MikeZ7/LF_Hammerhead/KiCAD/LF_HAMMERHEAD_schematics.kicad_sch

## KiCad design KiCAD/LF_HAMMERHEAD_schematics.kicad_sch (2023-11-29)

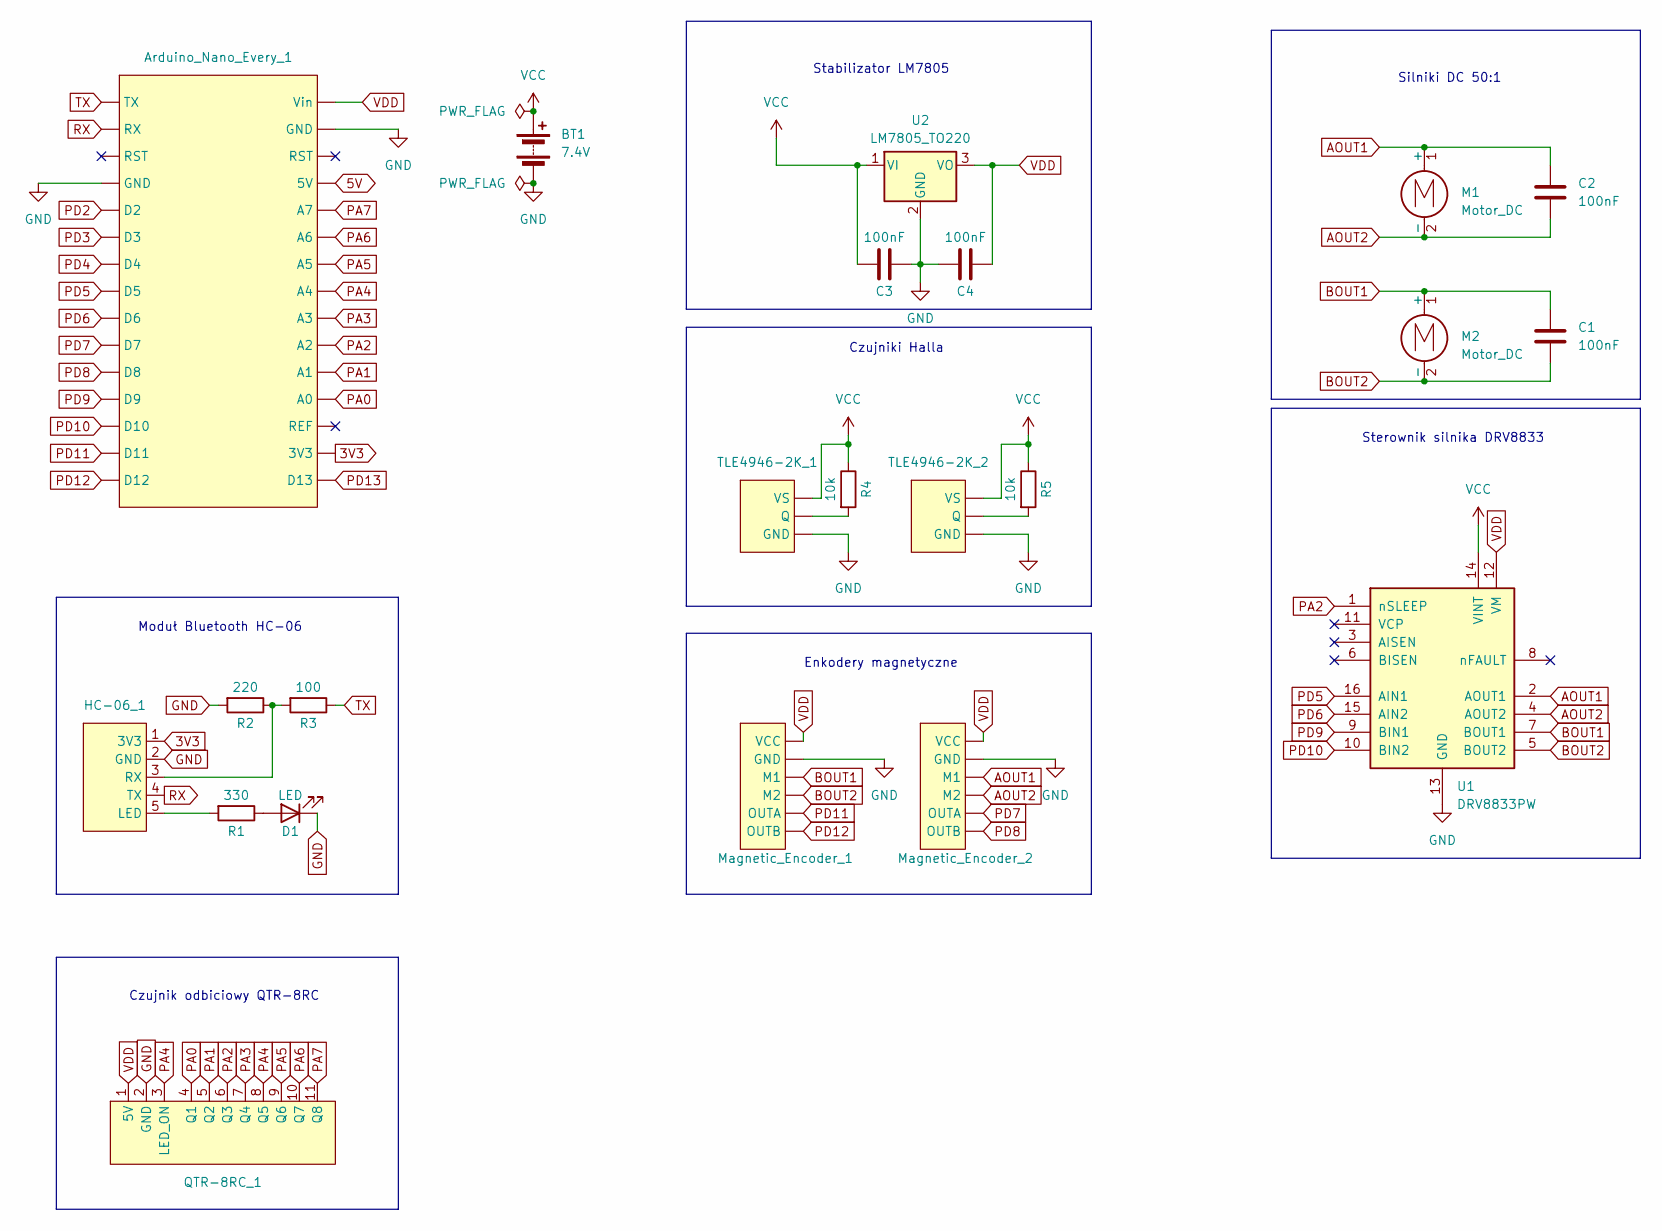
[picture p8: schematic LF_HAMMERHEAD_schematics.kicad_sch]

Parts:
Arduino_Nano_Every_1: (no value)
BT1: 7.4V
C1, C2, C3, C4: 100nF
D1: LED
HC-06_1: (no value)
M1, M2: Motor_DC
Magnetic_Encoder_1, Magnetic_Encoder_2: (no value)
QTR-8RC_1: (no value)
R1: 330
R2: 220
R3: 100
R4, R5: 10k
TLE4946-2K_1, TLE4946-2K_2: (no value)
U1: DRV8833PW; TSSOP-16_4.4x5mm_P0.65mm
U2: LM7805_TO220; TO-220-3_Vertical

Connections:
3V3: Arduino_Nano_Every_1., HC-06_1.1 (3V3)
5V: Arduino_Nano_Every_1.
AOUT1: C2.1, M1.1 (+), Magnetic_Encoder_2., U1.2 (AOUT1)
AOUT2: C2.2, M1.2 (-), Magnetic_Encoder_2., U1.4 (AOUT2)
BOUT1: C1.1, M2.1 (+), Magnetic_Encoder_1., U1.7 (BOUT1)
BOUT2: C1.2, M2.2 (-), Magnetic_Encoder_1., U1.5 (BOUT2)
GND: Arduino_Nano_Every_1., BT1.2 (-), C3.2, C4.1, D1.1 (K), HC-06_1.2 (GND), Magnetic_Encoder_1., Magnetic_Encoder_2., QTR-8RC_1.2 (GND), R2.2, TLE4946-2K_1., TLE4946-2K_2., U1.13 (GND), U2.2 (GND)
unnamed: D1.2 (A), R1.1
unnamed: HC-06_1.3 (RX), R2.1, R3.2
unnamed: HC-06_1.5 (LED), R1.2
unnamed: R4.2, TLE4946-2K_1.
unnamed: R5.2, TLE4946-2K_2.
PA0: Arduino_Nano_Every_1., QTR-8RC_1.4 (Q1)
PA1: Arduino_Nano_Every_1., QTR-8RC_1.5 (Q2)
PA2: Arduino_Nano_Every_1., QTR-8RC_1.6 (Q3), U1.1 (nSLEEP)
PA3: Arduino_Nano_Every_1., QTR-8RC_1.7 (Q4)
PA4: Arduino_Nano_Every_1., QTR-8RC_1.3 (LED_ON), QTR-8RC_1.8 (Q5)
PA5: Arduino_Nano_Every_1., QTR-8RC_1.9 (Q6)
PA6: Arduino_Nano_Every_1., QTR-8RC_1.10 (Q7)
PA7: Arduino_Nano_Every_1., QTR-8RC_1.11 (Q8)
PD2: Arduino_Nano_Every_1.
PD3: Arduino_Nano_Every_1.
PD4: Arduino_Nano_Every_1.
PD5: Arduino_Nano_Every_1., U1.16 (AIN1)
PD6: Arduino_Nano_Every_1., U1.15 (AIN2)
PD7: Arduino_Nano_Every_1., Magnetic_Encoder_2.
PD8: Arduino_Nano_Every_1., Magnetic_Encoder_2.
PD9: Arduino_Nano_Every_1., U1.9 (BIN1)
PD10: Arduino_Nano_Every_1., U1.10 (BIN2)
PD11: Arduino_Nano_Every_1., Magnetic_Encoder_1.
PD12: Arduino_Nano_Every_1., Magnetic_Encoder_1.
PD13: Arduino_Nano_Every_1.
RX: Arduino_Nano_Every_1., HC-06_1.4 (TX)
TX: Arduino_Nano_Every_1., R3.1
VCC: BT1.1 (+), C3.1, R4.1, R5.1, TLE4946-2K_1., TLE4946-2K_2., U1.14 (VINT), U2.1 (VI)
VDD: Arduino_Nano_Every_1., C4.2, Magnetic_Encoder_1., Magnetic_Encoder_2., QTR-8RC_1.1 (5V), U1.12 (VM), U2.3 (VO)

Notes on the sheet:
Enkodery magnetyczne
Czujniki Halla
Moduł Bluetooth HC-06
Silniki DC 50:1
Czujnik odbiciowy QTR-8RC
Sterownik silnika DRV8833
Stabilizator LM7805
